knightfox75/PS2_Mouse_to_Serial_Port/media/in-a-box prototype/in-a-box-prototype_04.jpg

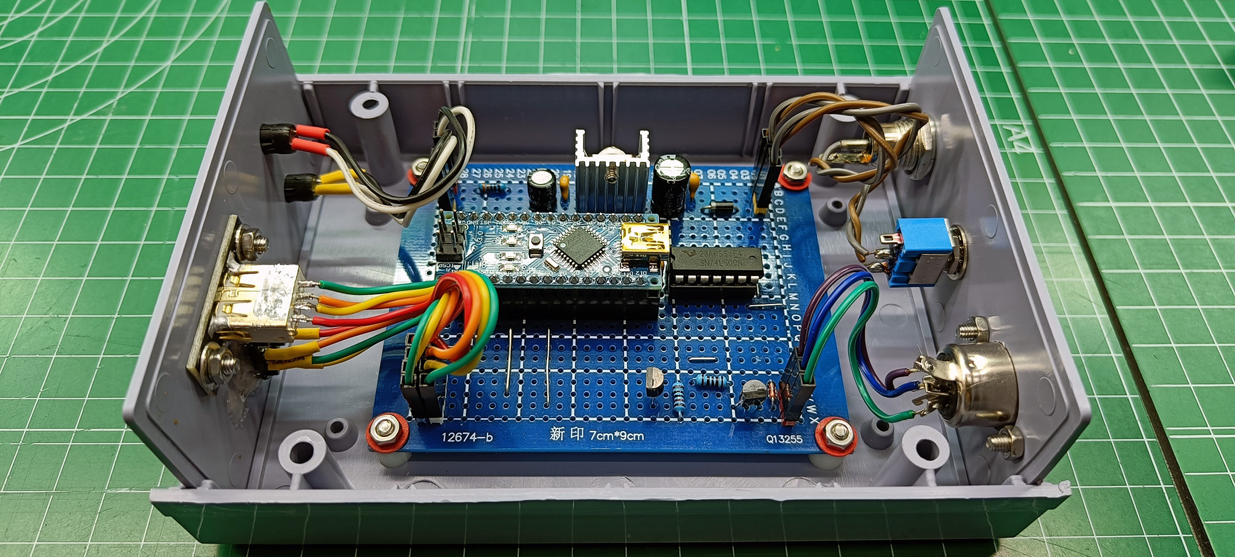
media/in-a-box prototype/in-a-box-prototype_04.jpg
