knightfox75/PS2_Mouse_to_Serial_Port/media/in-a-box/in-a-box_02.jpg

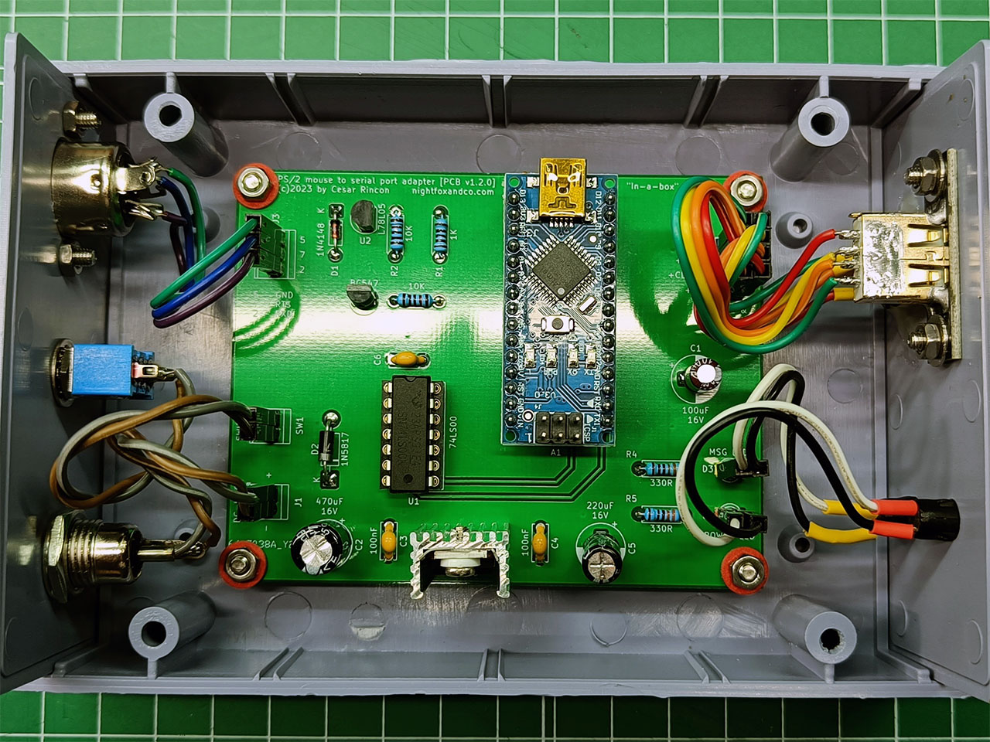
media/in-a-box/in-a-box_02.jpg
