knightfox75/PS2_Mouse_to_Serial_Port/media/isa card/isa_04.jpg

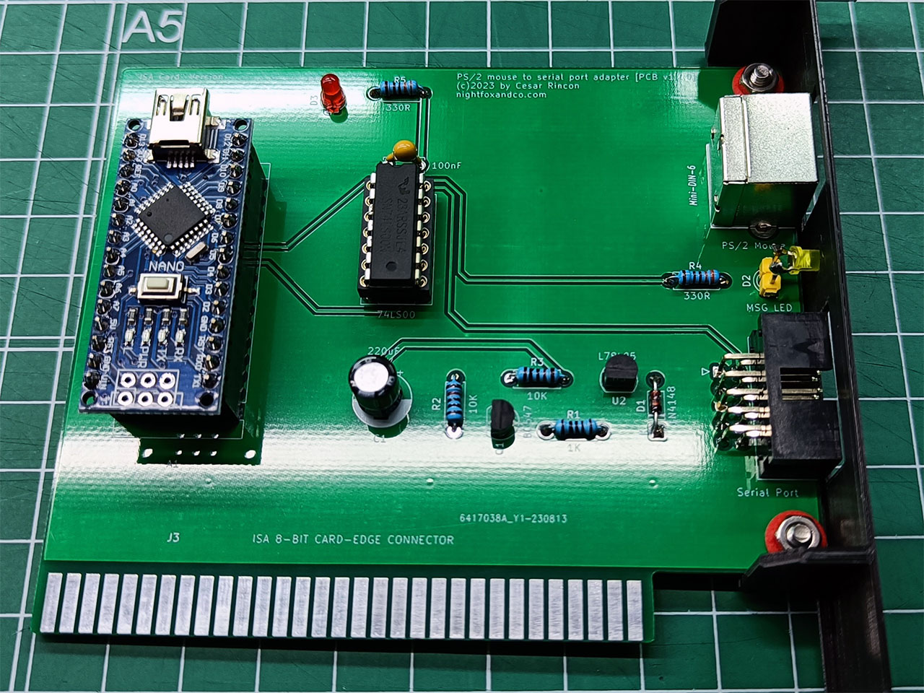
media/isa card/isa_04.jpg
