knightfox75/PS2_Mouse_to_Serial_Port/schematics/In_a_Box/Schematic/ps2_mouse_to_serial_port_adapter_in_a_box.png

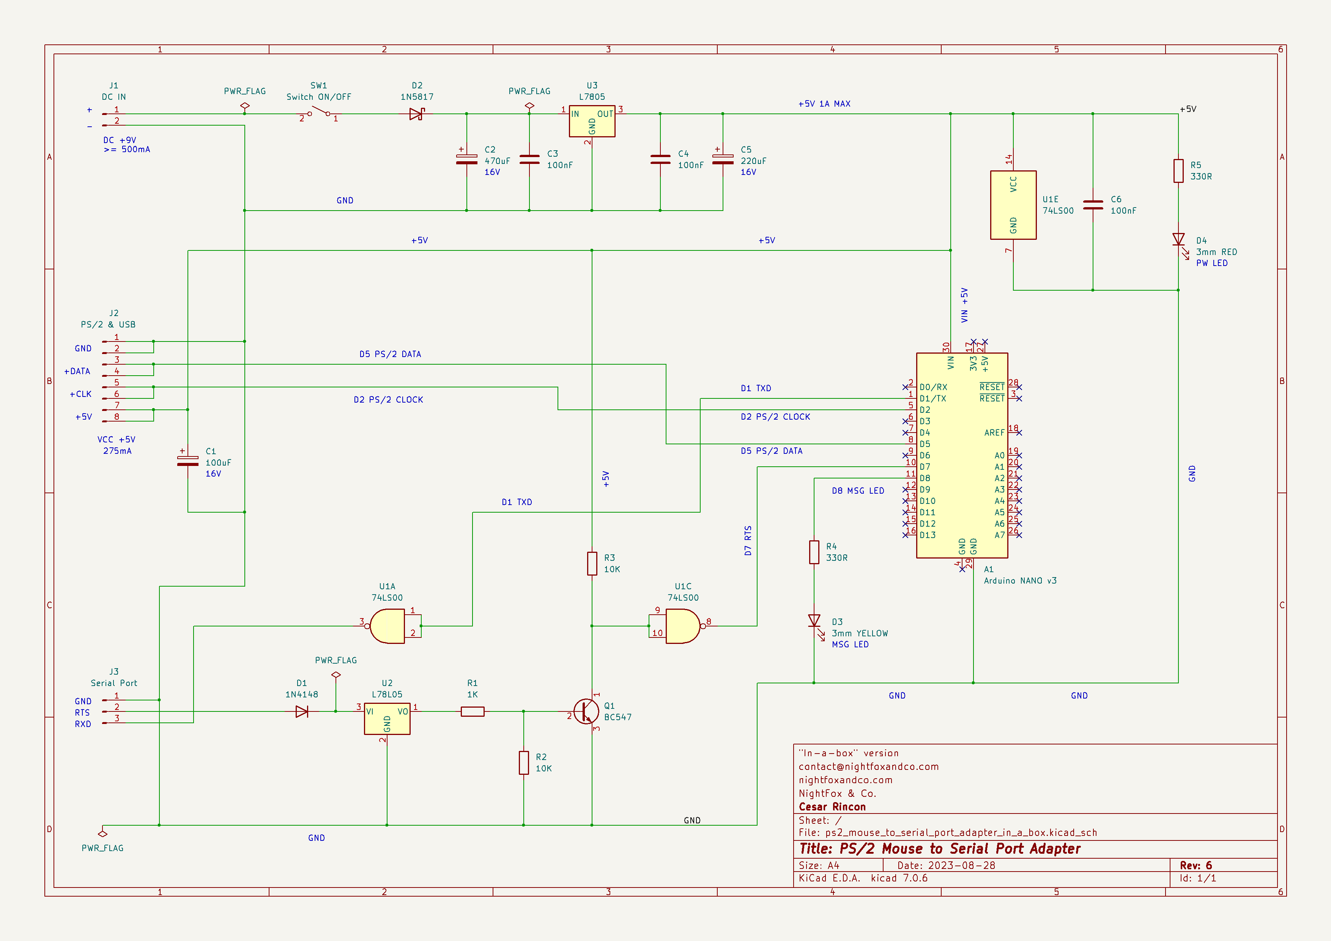
schematics/In_a_Box/Schematic/ps2_mouse_to_serial_port_adapter_in_a_box.png
