knightfox75/PS2_Mouse_to_Serial_Port/schematics/ISA_Card/PBC_preview/ps2_mouse_to_serial_port_adapter_ISA_card_back.png

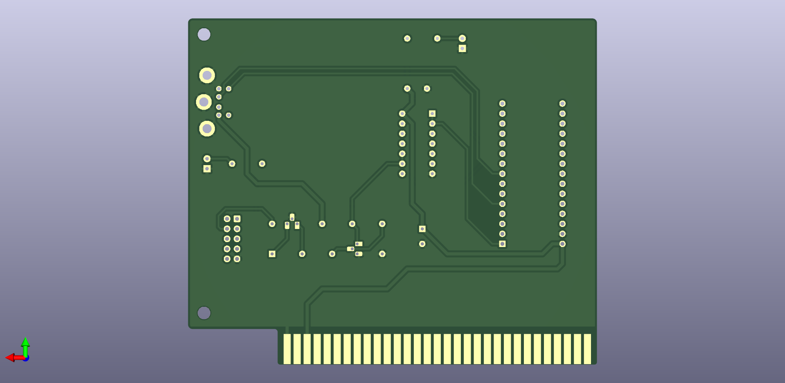
schematics/ISA_Card/PBC_preview/ps2_mouse_to_serial_port_adapter_ISA_card_back.png
