knightfox75/PS2_Mouse_to_Serial_Port/schematics/ISA_Card/Schematic/ps2_mouse_to_serial_port_adapter_ISA_card.png

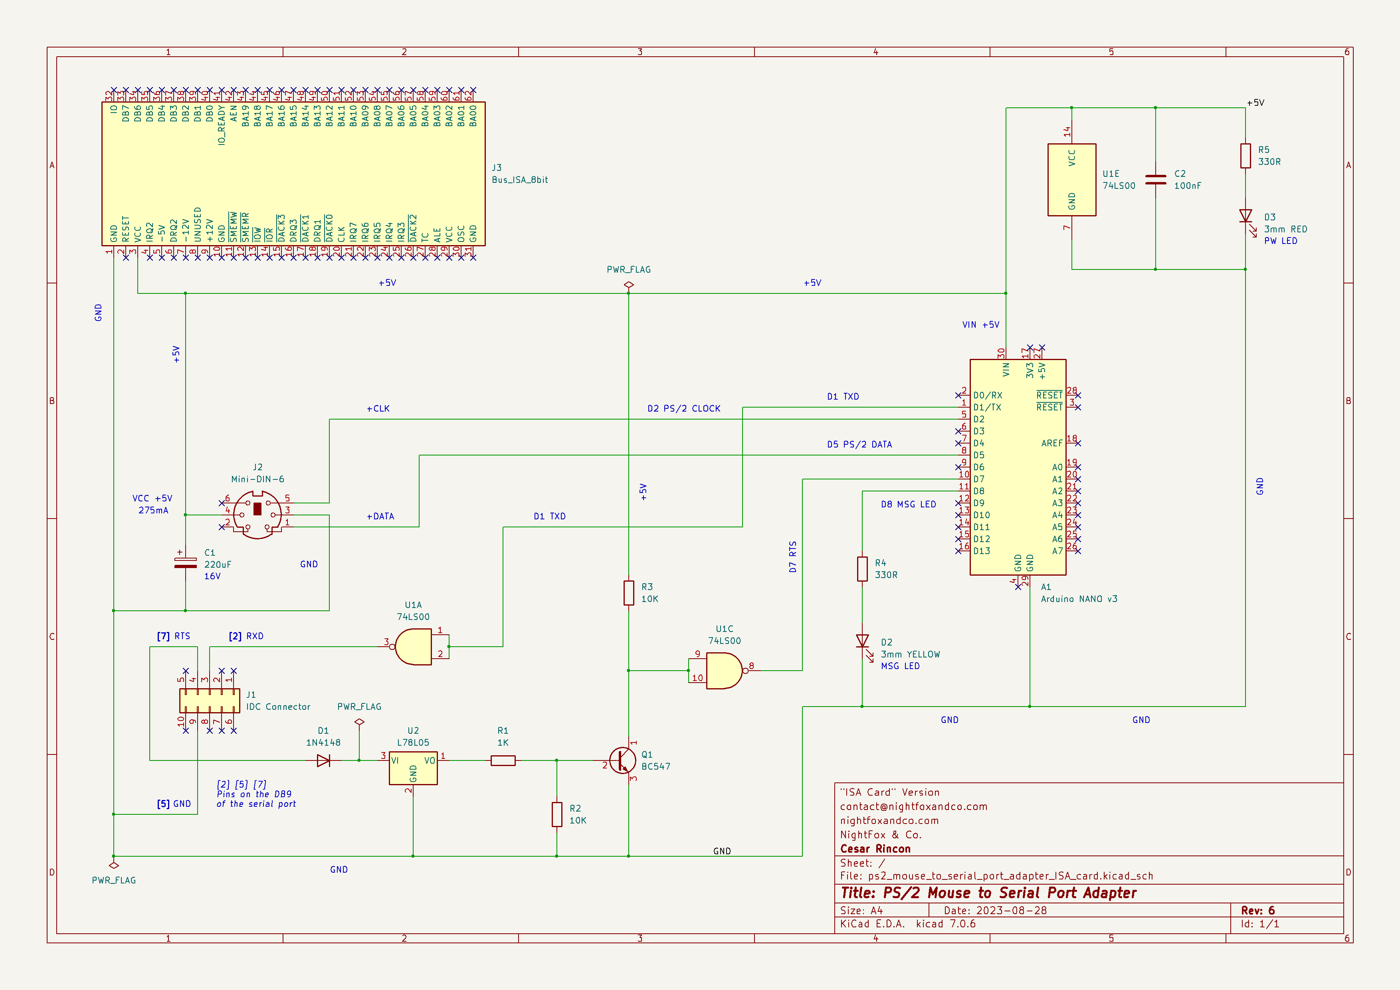
schematics/ISA_Card/Schematic/ps2_mouse_to_serial_port_adapter_ISA_card.png
