knightfox75/PS2_Mouse_to_Serial_Port/schematics/Stand_Alone/PBC_preview/ps2_mouse_to_serial_port_adapter_stand_alone_front.png

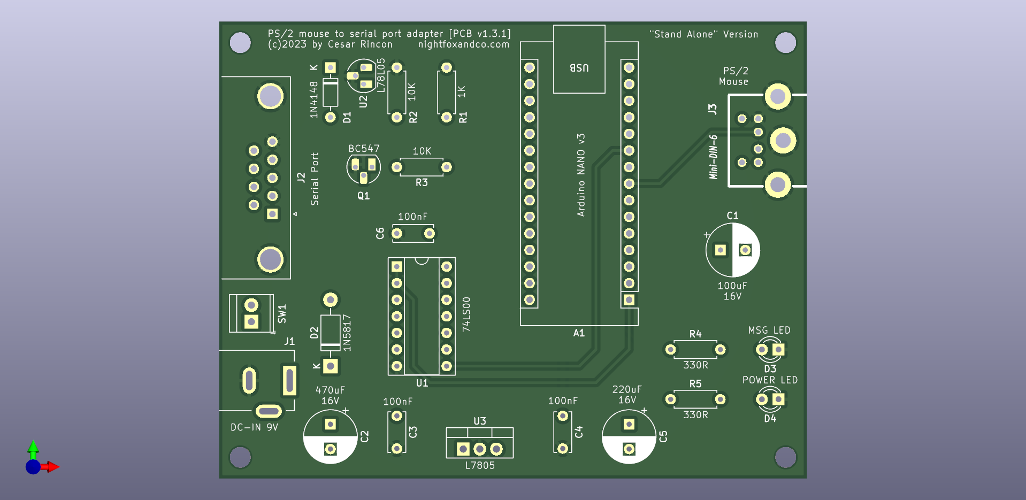
schematics/Stand_Alone/PBC_preview/ps2_mouse_to_serial_port_adapter_stand_alone_front.png
