knightfox75/PS2_Mouse_to_Serial_Port/schematics/KiCad/ps2_mouse_to_serial_rev_1_2.kicad_sch

## KiCad design schematics/KiCad/ps2_mouse_to_serial_rev_1_2.kicad_sch (2023-08-09)

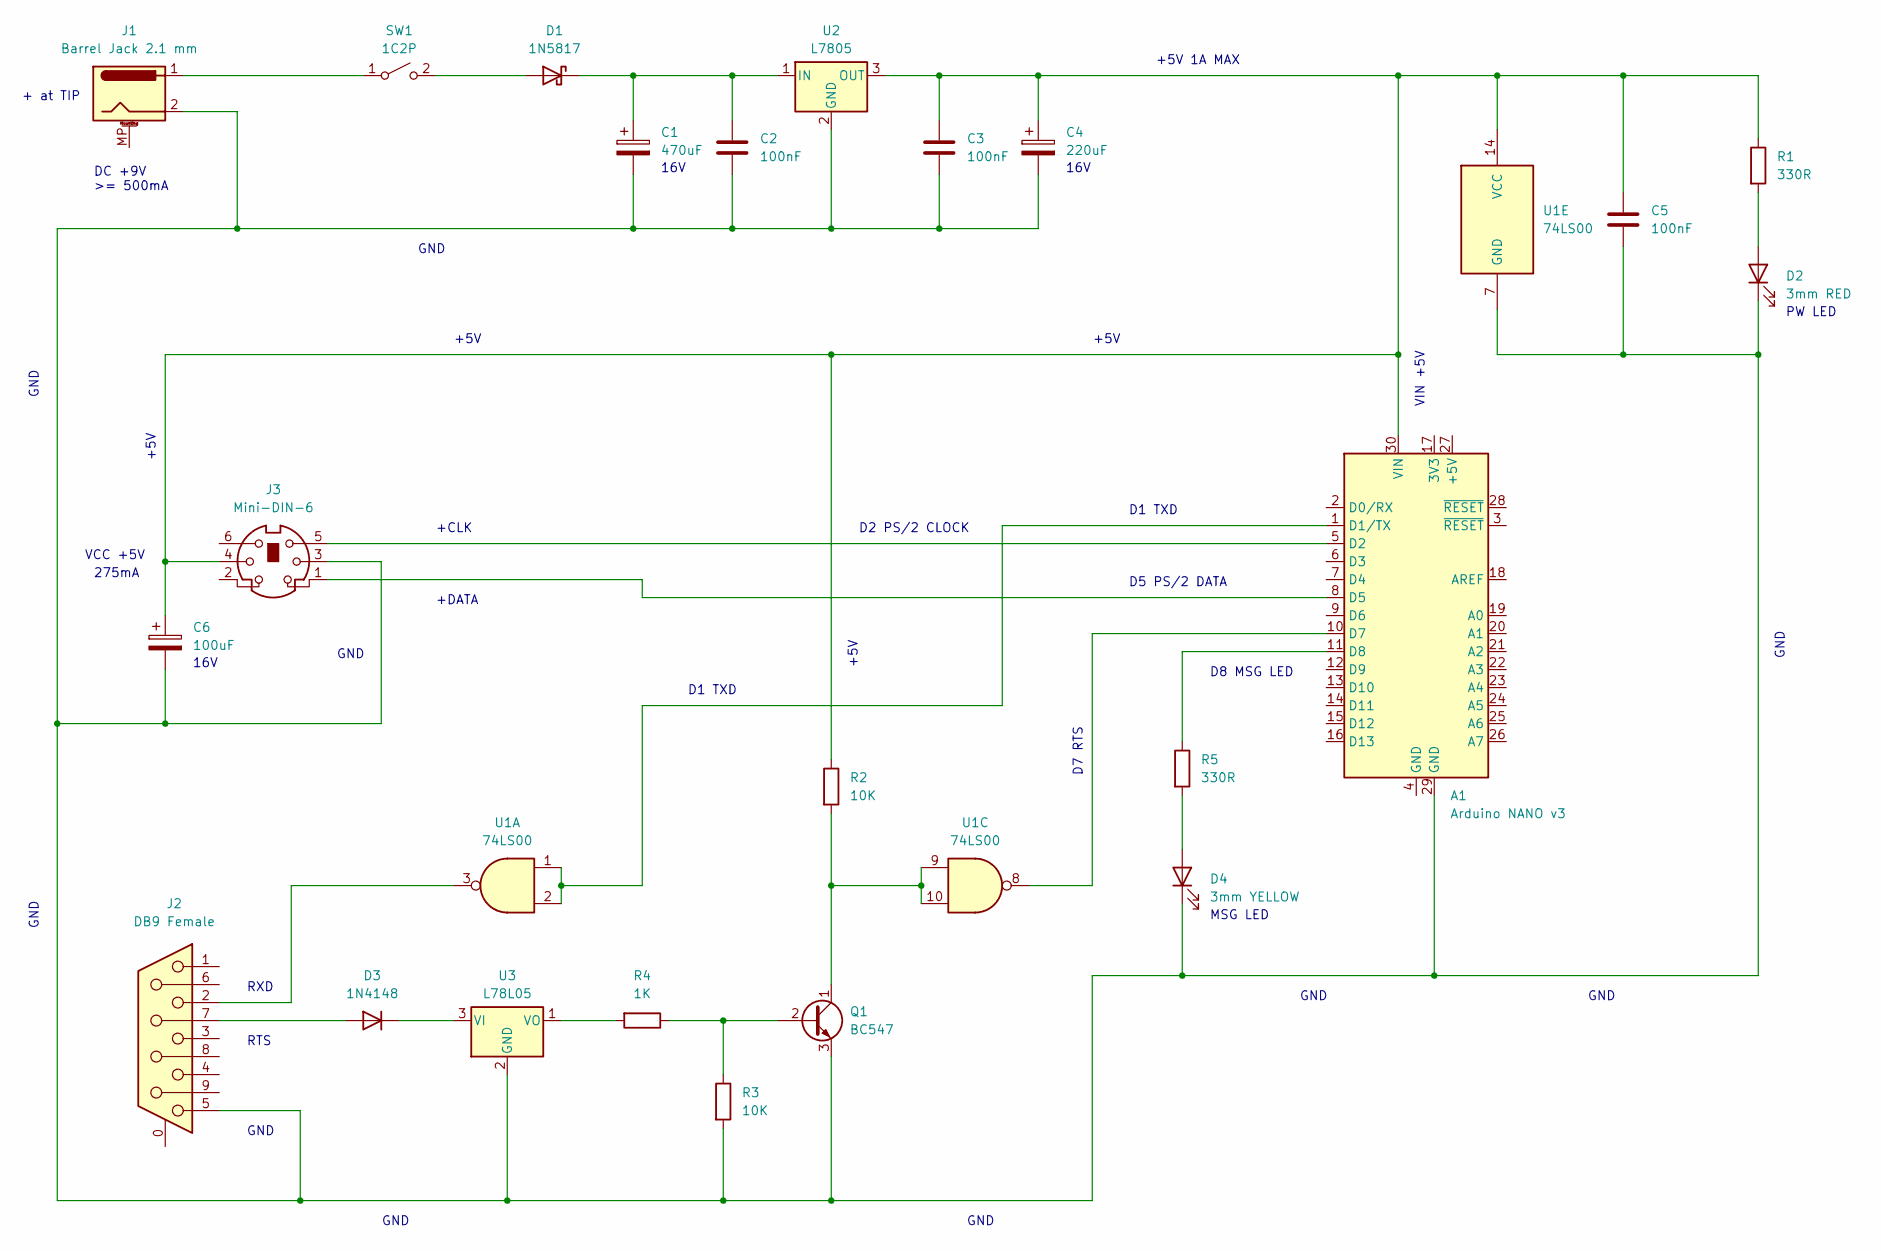
[picture p40: schematic ps2_mouse_to_serial_rev_1_2.kicad_sch]

Parts:
A1: Arduino NANO v3; Arduino_Nano
C1: 470uF; CP_Radial_D8.0mm_P3.80mm
C2, C3, C5: 100nF; C_Disc_D6.0mm_W2.5mm_P5.00mm
C4: 220uF; CP_Radial_D8.0mm_P3.80mm
C6: 100uF; CP_Radial_D8.0mm_P3.80mm
D1: 1N5817; D_DO-41_SOD81_P10.16mm_Horizontal
D2: 3mm RED
D3: 1N4148; D_DO-35_SOD27_P7.62mm_Horizontal
D4: 3mm YELLOW
J1: Barrel Jack 2.1 mm; BarrelJack_CUI_PJ-063AH_Horizontal
J2: DB9 Female
J3: Mini-DIN-6
Q1: BC547; TO-92_Inline
R1, R5: 330R; R_Axial_DIN0207_L6.3mm_D2.5mm_P7.62mm_Horizontal
R2, R3: 10K; R_Axial_DIN0207_L6.3mm_D2.5mm_P7.62mm_Horizontal
R4: 1K; R_Axial_DIN0207_L6.3mm_D2.5mm_P7.62mm_Horizontal
SW1: 1C2P
U1: 74LS00
U2: L7805; TO-220-3_Vertical
U3: L78L05; TO-92_Inline

Connections:
unnamed: A1.1 (D1/TX), U1.1, U1.2
unnamed: A1.5 (D2), J3.5
unnamed: A1.8 (D5), J3.1
unnamed: A1.10 (D7), U1.8
unnamed: A1.11 (D8), R5.1
unnamed: A1.29 (GND), C1.2, C2.2, C3.2, C4.2, C5.2, C6.2, D2.1 (K), D4.1 (K), J1.2, J2.5, J3.3, Q1.3 (E), R3.2, U1.7 (GND), U2.2 (GND), U3.2 (GND)
unnamed: A1.30 (VIN), C3.1, C4.1, C5.1, C6.1, J3.4, R1.1, R2.1, U1.14 (VCC), U2.3 (OUT)
unnamed: C1.1, C2.1, D1.1 (K), U2.1 (IN)
unnamed: D1.2 (A), SW1.2 (B)
unnamed: D2.2 (A), R1.2
unnamed: D3.1 (K), U3.3 (VI)
unnamed: D3.2 (A), J2.7
unnamed: D4.2 (A), R5.2
unnamed: J1.1, SW1.1 (A)
unnamed: J2.2, U1.3
unnamed: Q1.1 (C), R2.2, U1.9, U1.10
unnamed: Q1.2 (B), R3.1, R4.1
unnamed: R4.2, U3.1 (VO)

Notes on the sheet:
+CLK
PW LED
GND
16V
VCC +5V
MSG LED
+5V
D8 MSG LED
DC +9V >= 500mA
RTS
D5 PS/2 DATA
D1 TXD
D2 PS/2 CLOCK
+ at TIP
VIN +5V
RXD
D7 RTS
+5V 1A MAX
+DATA
275mA
